VoxoTech/PiDAR/_experiments/sphere.py

# https://www.tutorialspoint.com/plotting-points-on-the-surface-of-a-sphere-in-python-s-matplotlib

import matplotlib.pyplot as plt
import numpy as np

# plt.rcParams["figure.figsize"] = [7.00, 3.50]
# plt.rcParams["figure.autolayout"] = True
fig = plt.figure()
ax = fig.add_subplot(projection='3d')

u, v = np.mgrid[0:2 * np.pi:5j, 0:np.pi:5j]
x = np.cos(u) * np.sin(v)
y = np.sin(u) * np.sin(v)
z = np.cos(v)

ax.scatter(x, y, z)
plt.show()
